herpiko/unk/images/finished-2.png

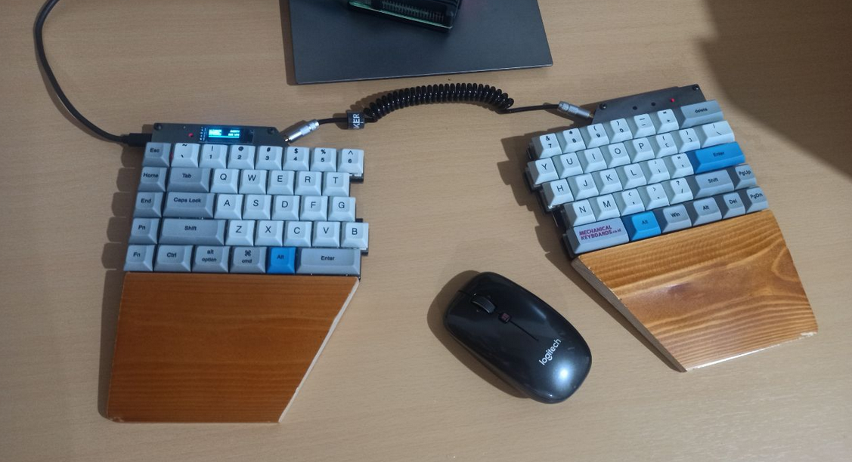
images/finished-2.png
