herpiko/unk/images/layout.png

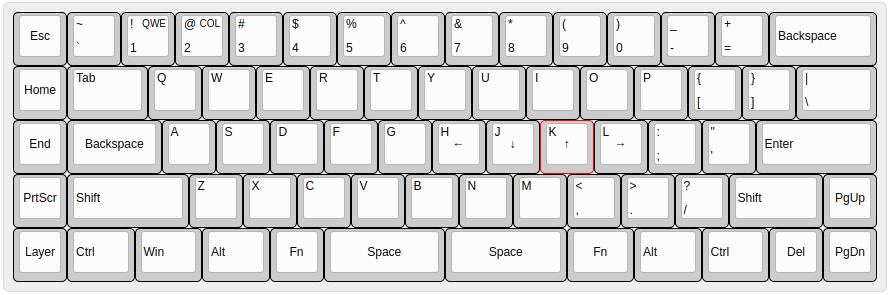
images/layout.png
