herpiko/unk/images/plate-2.jpg

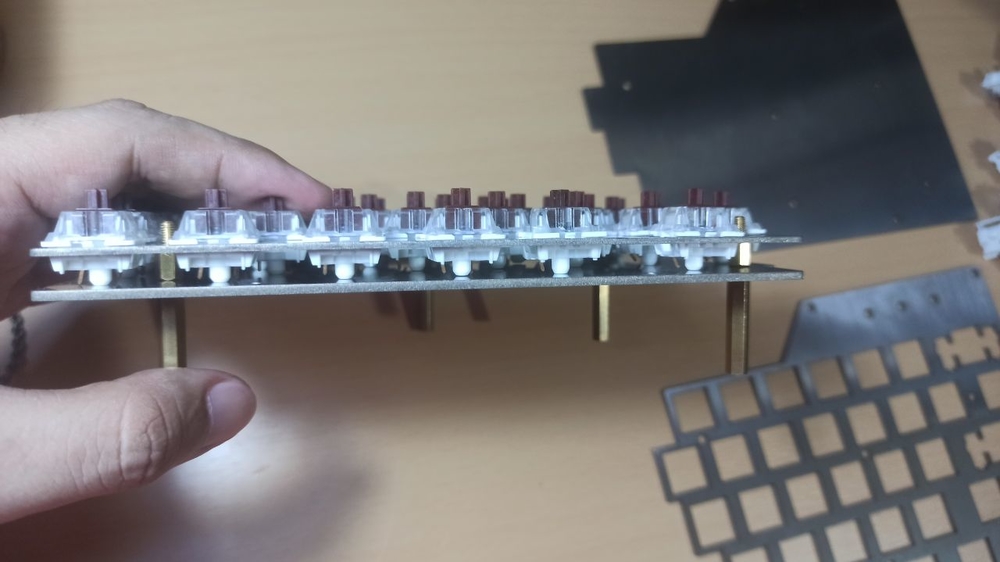
images/plate-2.jpg
